wuphilipp/gello_mechanical/gripper/trigger.STL

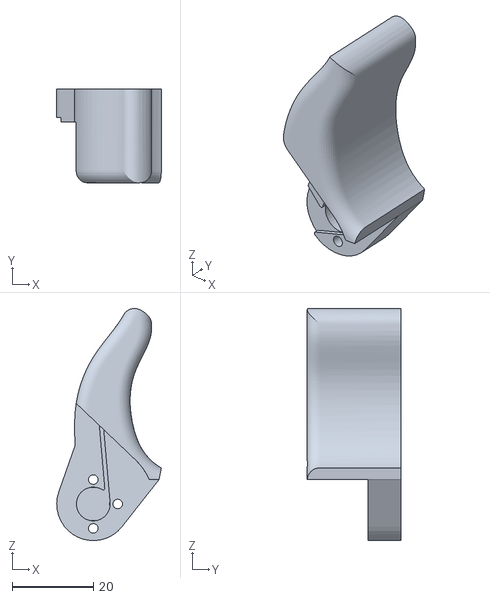
[picture p20: CAD file, 2023-11-06]
gripper/trigger.STL
25.7 x 23.0 x 57.0
