wuphilipp/gello_mechanical/lite6/3dprint_parts/baseRoll.stl

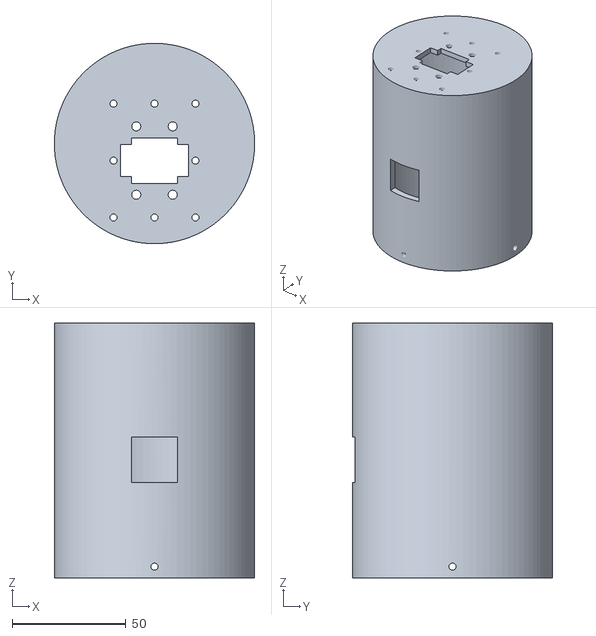
[picture p21: CAD file, 2024-01-16]
lite6/3dprint_parts/baseRoll.stl
88.0 x 88.0 x 112.0
