wuphilipp/gello_mechanical/yam/yam_passive_gello_small/L2.stl

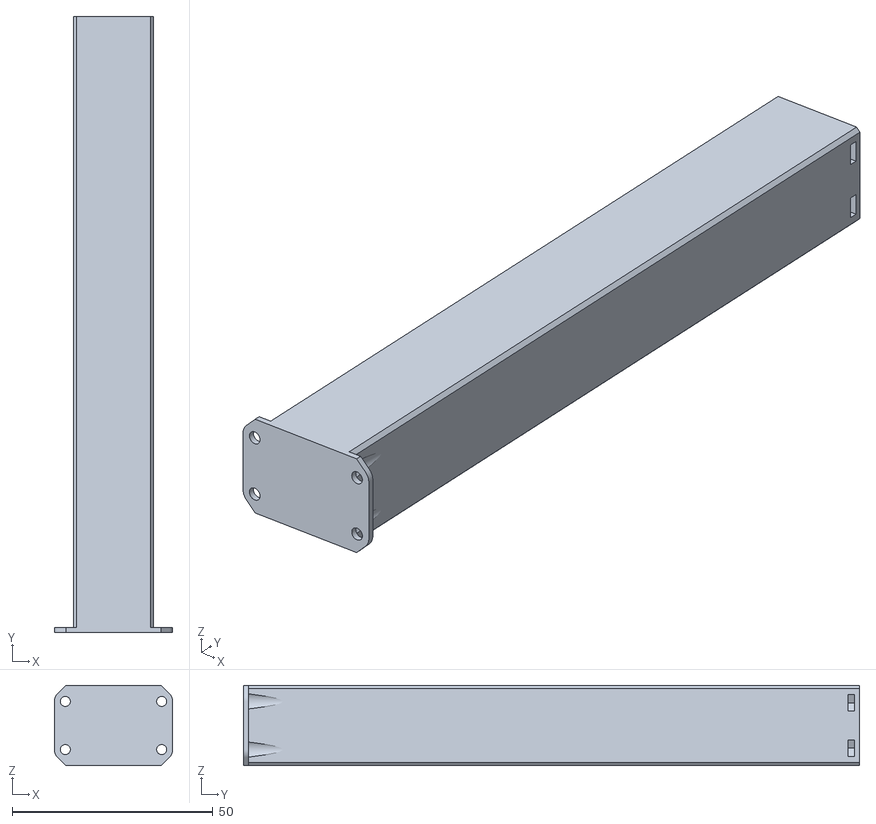
[picture p22: CAD file, 2025-08-02]
yam/yam_passive_gello_small/L2.stl
29.5 x 153.5 x 20.0
