wuphilipp/gello_mechanical/ar4/3dprint_parts/wrist.stl

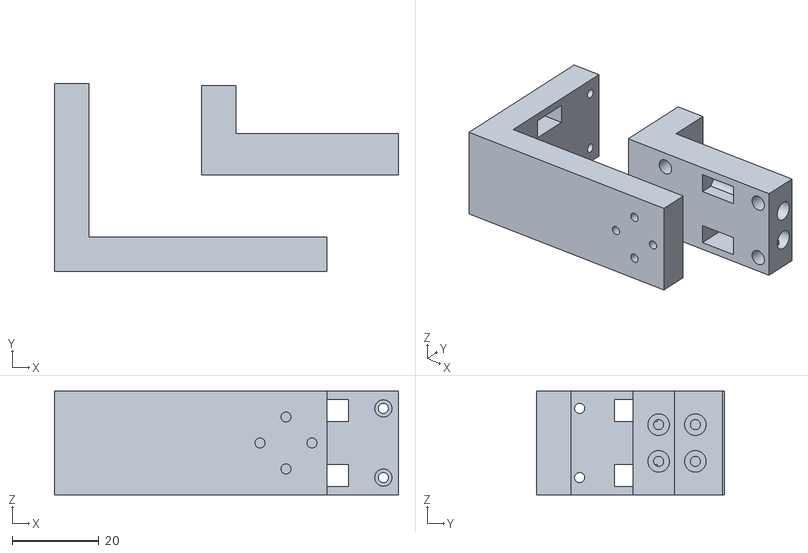
[picture p23: CAD file, 2024-03-06]
ar4/3dprint_parts/wrist.stl
79.5 x 43.5 x 24.0
