wuphilipp/gello_mechanical/franka_fer/base.STL

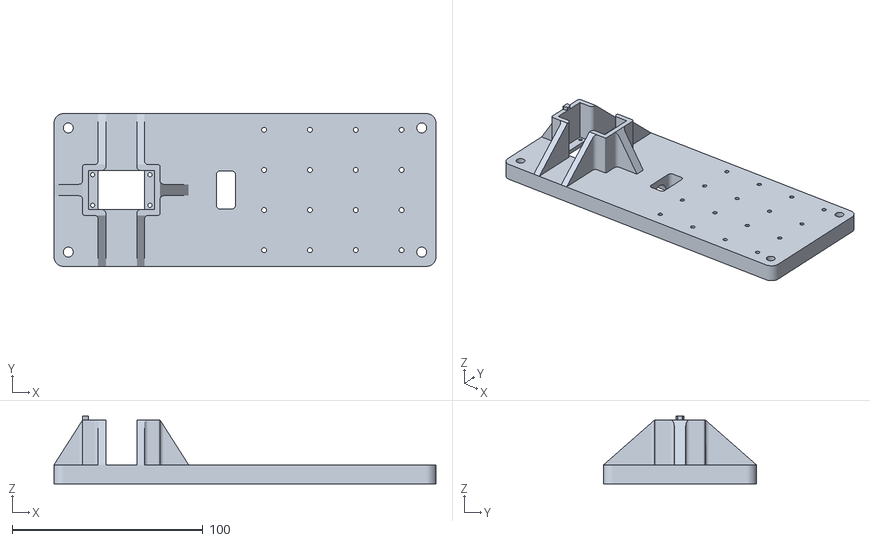
[picture p24: CAD file, 2023-11-06]
franka_fer/base.STL
200.0 x 80.0 x 35.5
