wuphilipp/gello_mechanical/franka_fr3/20_TRIGGER_BODY.STL

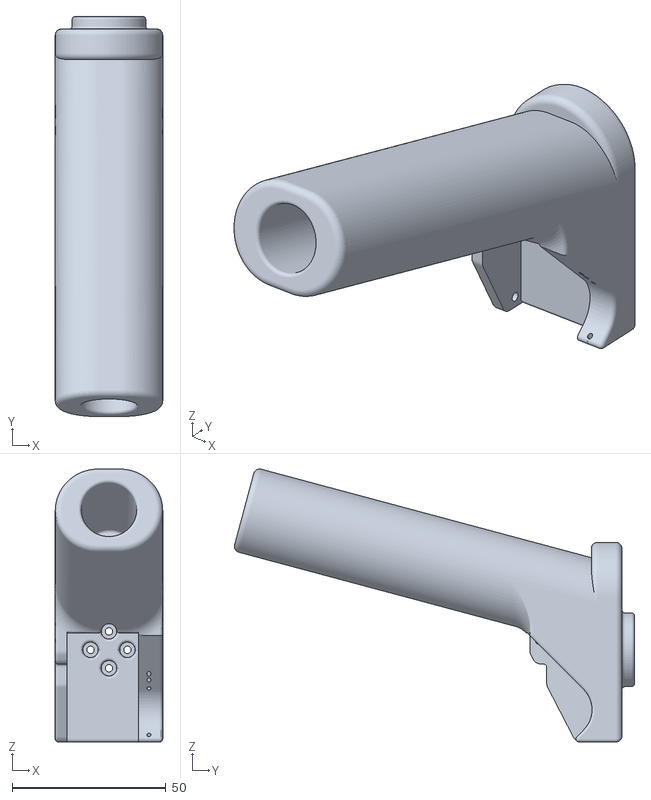
[picture p25: CAD file, 2026-04-10]
franka_fr3/20_TRIGGER_BODY.STL
35.0 x 130.2 x 88.8
