wuphilipp/gello_mechanical/lite6/3dprint_parts/baseBottom.stl

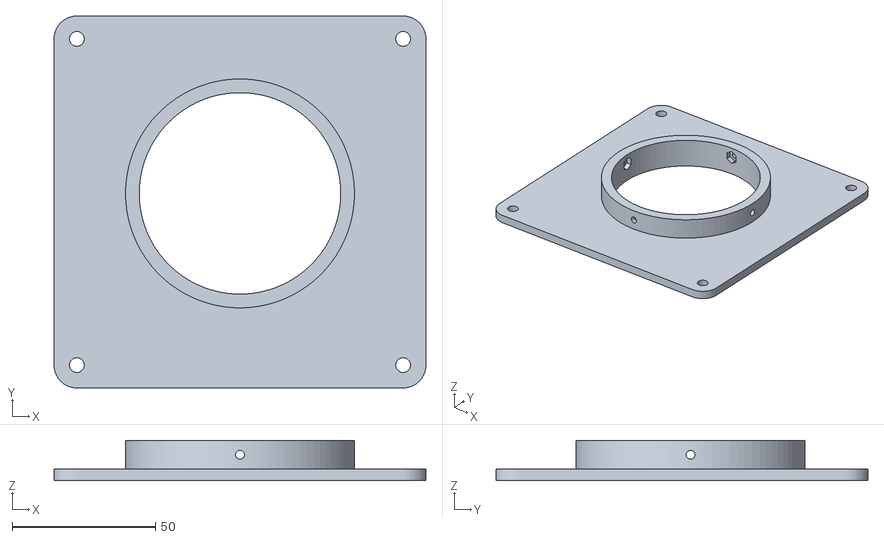
[picture p26: CAD file, 2024-01-16]
lite6/3dprint_parts/baseBottom.stl
130.0 x 130.0 x 14.0
