wuphilipp/gello_mechanical/ar4/3dprint_parts/l1.stl

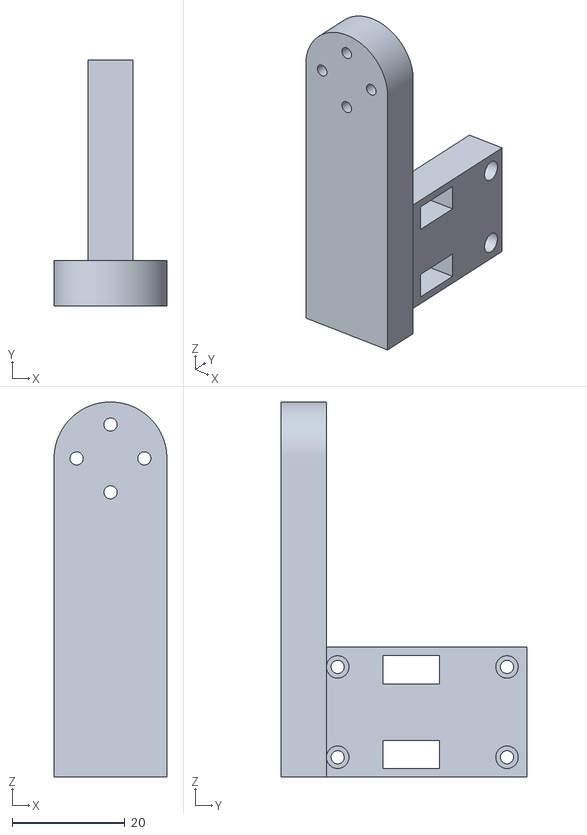
[picture p27: CAD file, 2024-03-06]
ar4/3dprint_parts/l1.stl
20.0 x 43.5 x 66.4
