wuphilipp/gello_mechanical/franka_fer/L2.STL

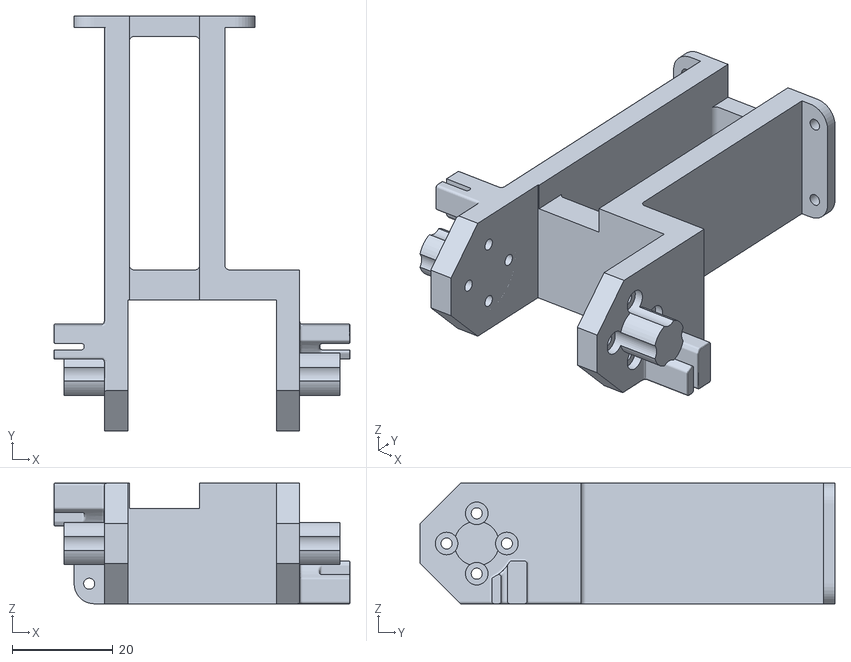
[picture p28: CAD file, 2023-11-06]
franka_fer/L2.STL
58.9 x 82.5 x 24.0
