wuphilipp/gello_mechanical/franka_fr3/02_BASE_BEARING.STL

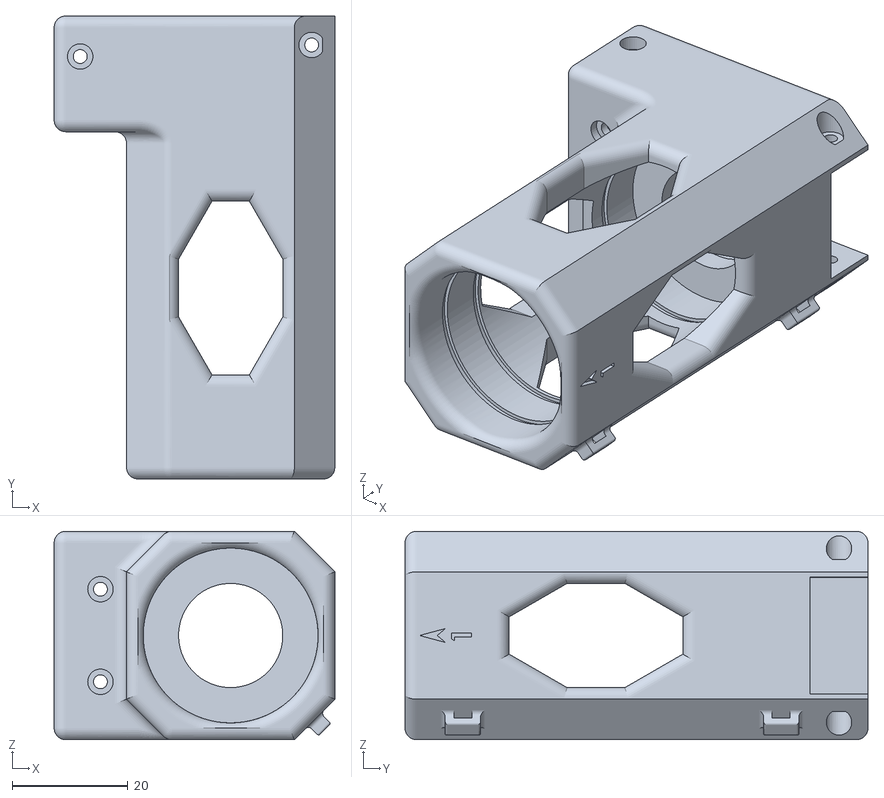
[picture p29: CAD file, 2026-04-10]
franka_fr3/02_BASE_BEARING.STL
48.5 x 80.0 x 36.0
