wuphilipp/gello_mechanical/lite6/3dprint_parts/L2.stl

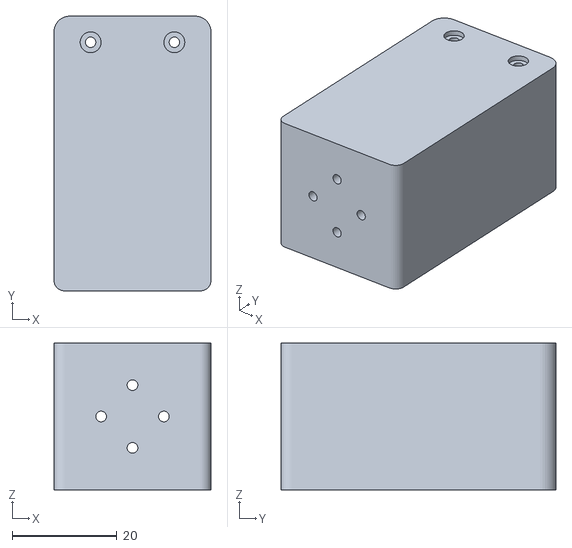
[picture p30: CAD file, 2024-01-16]
lite6/3dprint_parts/L2.stl
30.0 x 52.5 x 28.0
