wuphilipp/gello_mechanical/yam/yam_active_gello/L1.stl

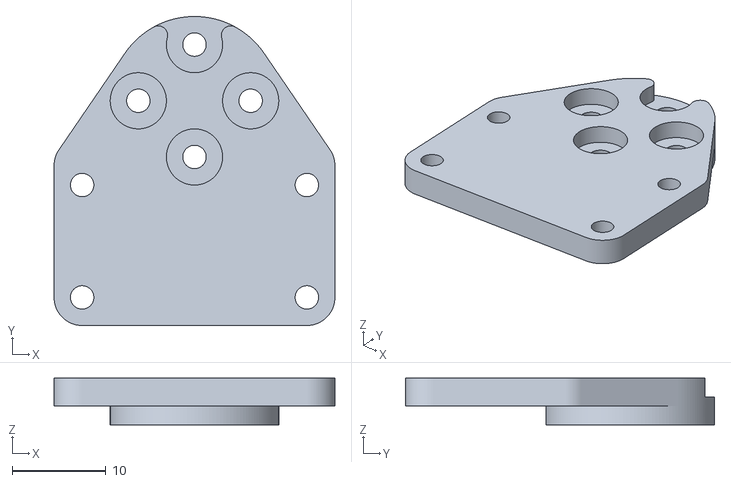
[picture p31: CAD file, 2025-08-02]
yam/yam_active_gello/L1.stl
30.0 x 33.0 x 5.00
