wuphilipp/gello_mechanical/yam/yam_passive_gello_small/L1.stl

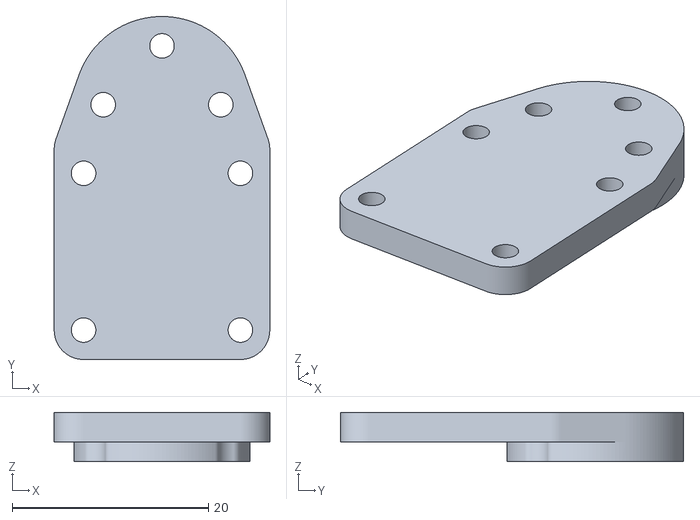
[picture p32: CAD file, 2025-08-02]
yam/yam_passive_gello_small/L1.stl
22.0 x 35.0 x 5.00
