wuphilipp/gello_mechanical/franka_fer/L4.STL

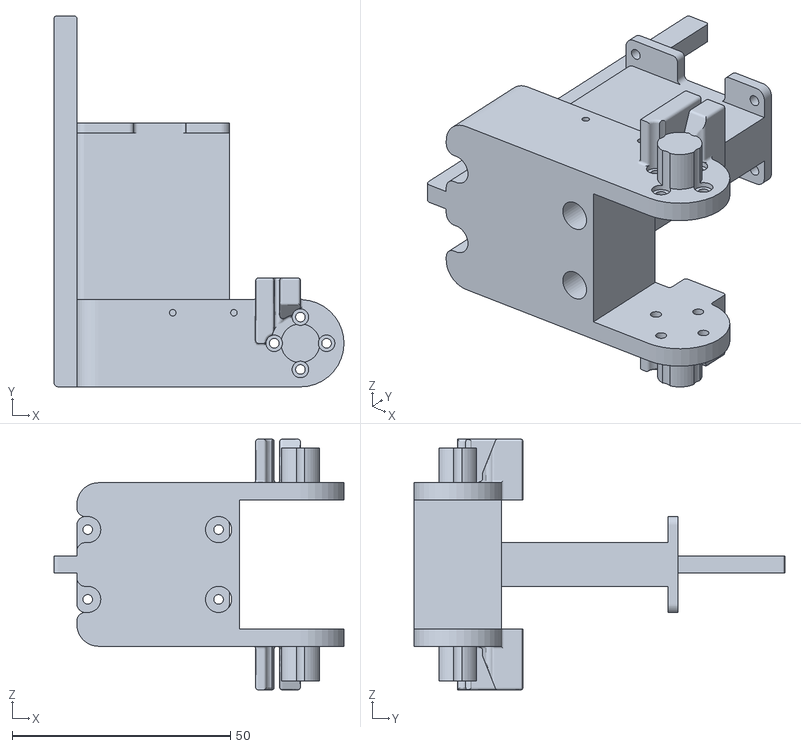
[picture p33: CAD file, 2023-11-06]
franka_fer/L4.STL
66.5 x 85.0 x 57.5
