wuphilipp/gello_mechanical/franka_fr3/11_MOTOR_SHAFT_UNIVERSAL.STL

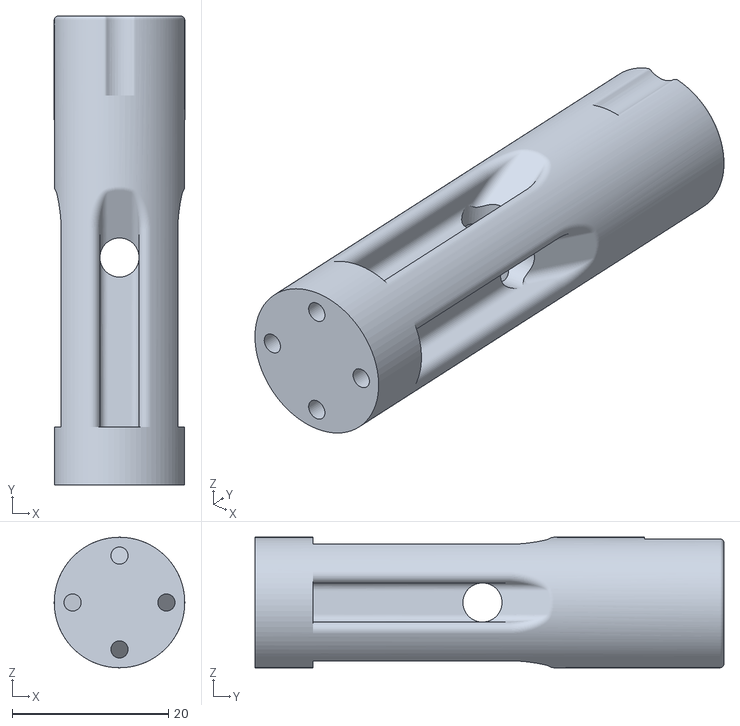
[picture p34: CAD file, 2026-04-10]
franka_fr3/11_MOTOR_SHAFT_UNIVERSAL.STL
16.7 x 60.0 x 16.7
