wuphilipp/gello_mechanical/lite6/3dprint_parts/base.stl

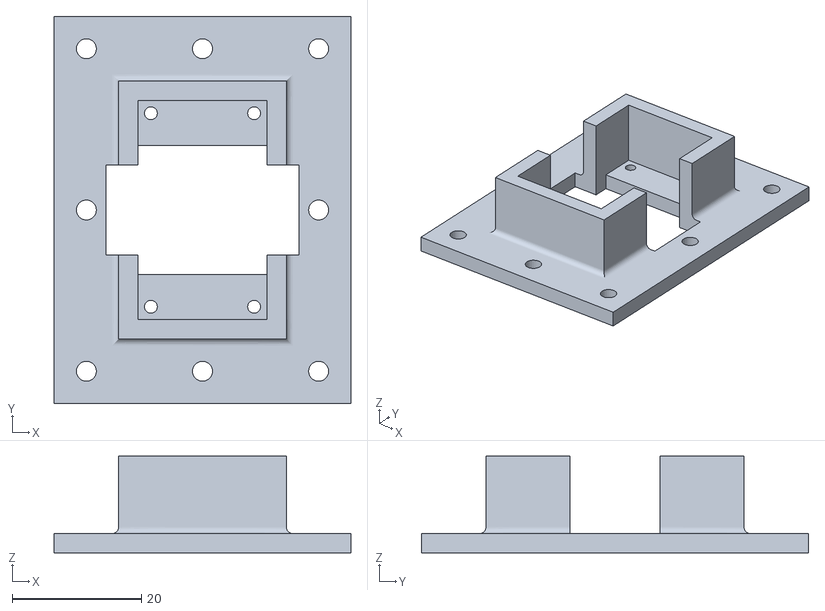
[picture p35: CAD file, 2024-01-16]
lite6/3dprint_parts/base.stl
46.0 x 60.0 x 15.0
