wuphilipp/gello_mechanical/yam/yam_active_gello/L2.stl

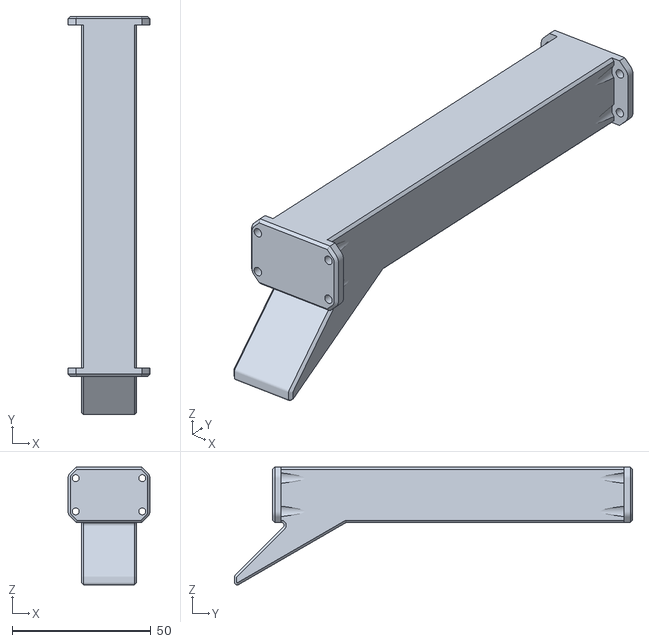
[picture p36: CAD file, 2025-08-02]
yam/yam_active_gello/L2.stl
29.5 x 143.5 x 42.5
