wuphilipp/gello_mechanical/ar4/3dprint_parts/arm2.stl

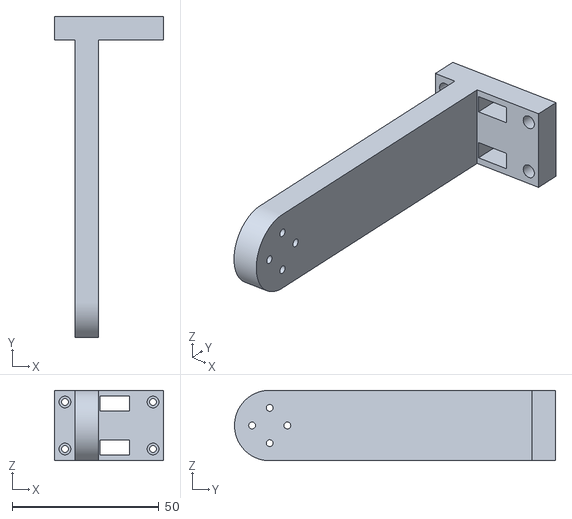
[picture p37: CAD file, 2024-03-06]
ar4/3dprint_parts/arm2.stl
37.0 x 109.3 x 24.0
