wuphilipp/gello_mechanical/franka_fer/L6.STL

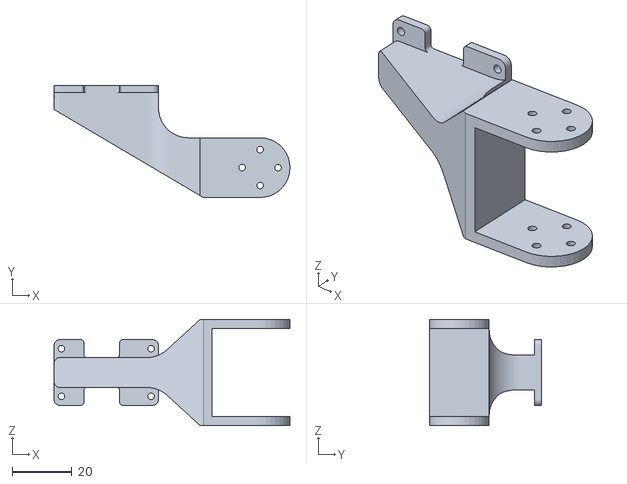
[picture p38: CAD file, 2023-11-06]
franka_fer/L6.STL
79.0 x 37.5 x 35.5
