wuphilipp/gello_mechanical/franka_fr3/03_A12_CONNECTOR.STL

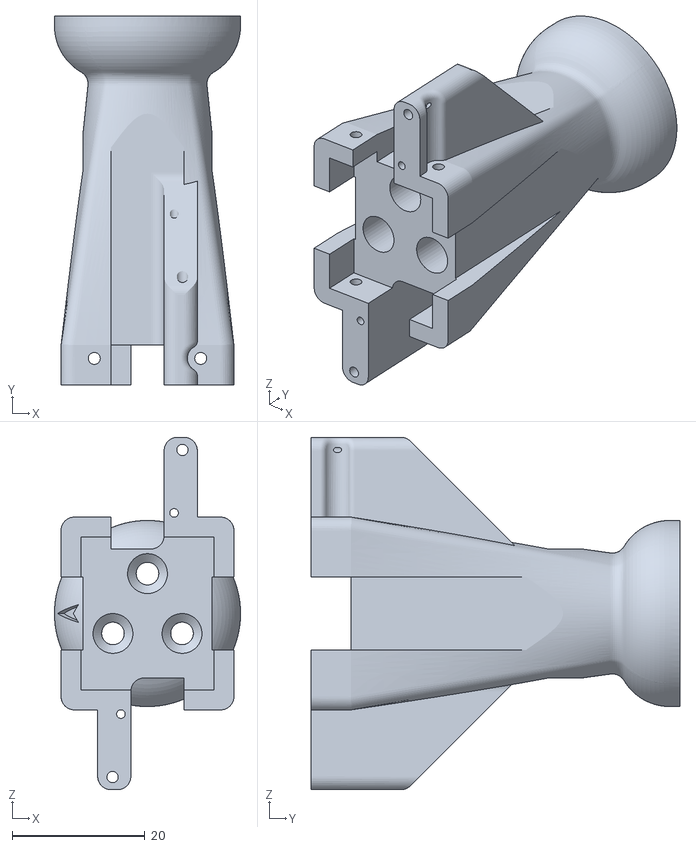
[picture p39: CAD file, 2026-04-10]
franka_fr3/03_A12_CONNECTOR.STL
28.0 x 55.5 x 53.0
