wuphilipp/gello_mechanical/lite6/3dprint_parts/L1.stl

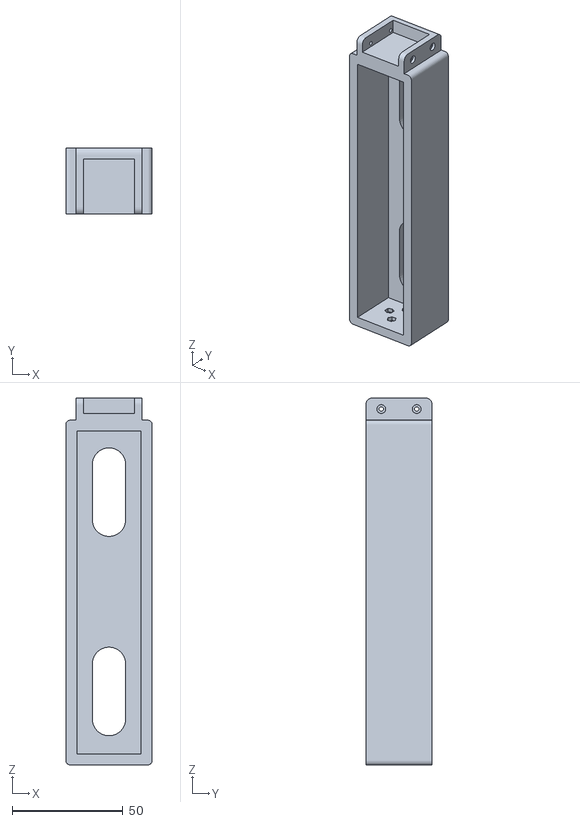
[picture p40: CAD file, 2024-01-16]
lite6/3dprint_parts/L1.stl
39.0 x 30.0 x 165.7
