wuphilipp/gello_mechanical/franka_fer/L3.STL

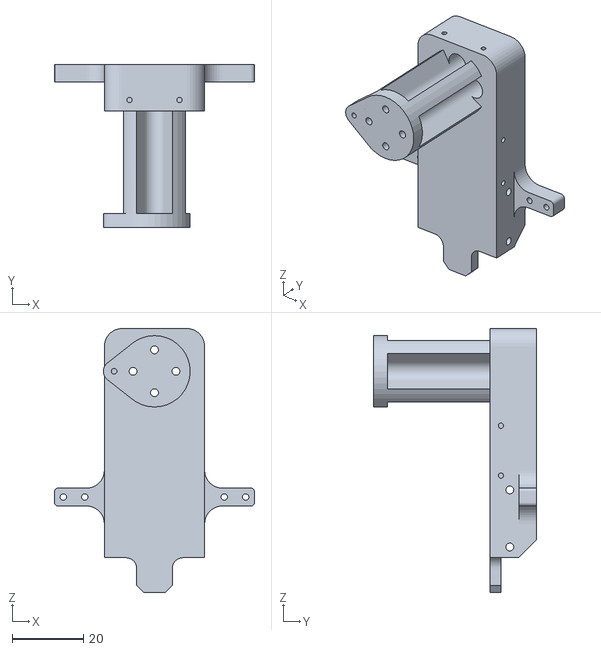
[picture p41: CAD file, 2023-11-06]
franka_fer/L3.STL
56.1 x 45.8 x 74.0
