wuphilipp/gello_mechanical/franka_fr3/21_TRIGGER_FINGER.STL

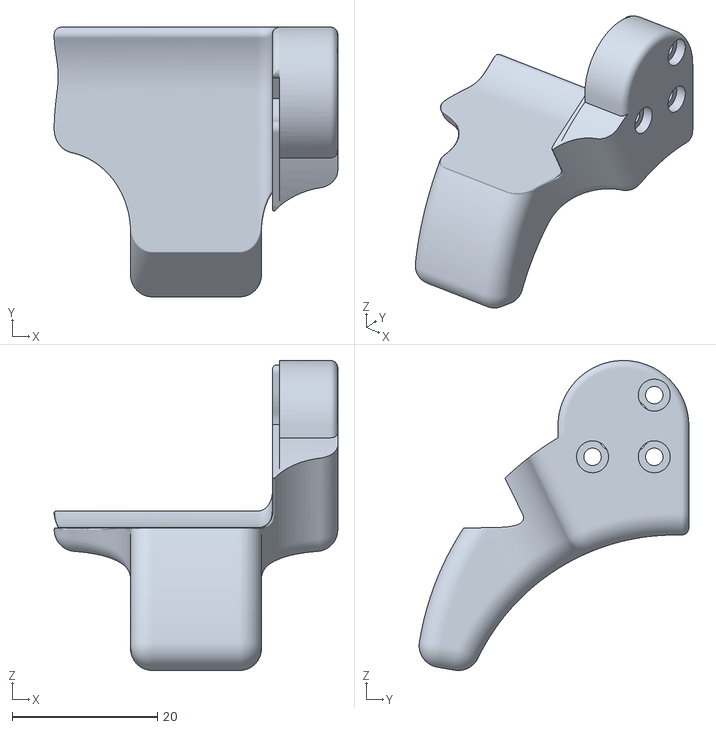
[picture p42: CAD file, 2026-04-10]
franka_fr3/21_TRIGGER_FINGER.STL
39.0 x 37.1 x 42.6
