wuphilipp/gello_mechanical/lite6/3dprint_parts/baseRollExtender.stl

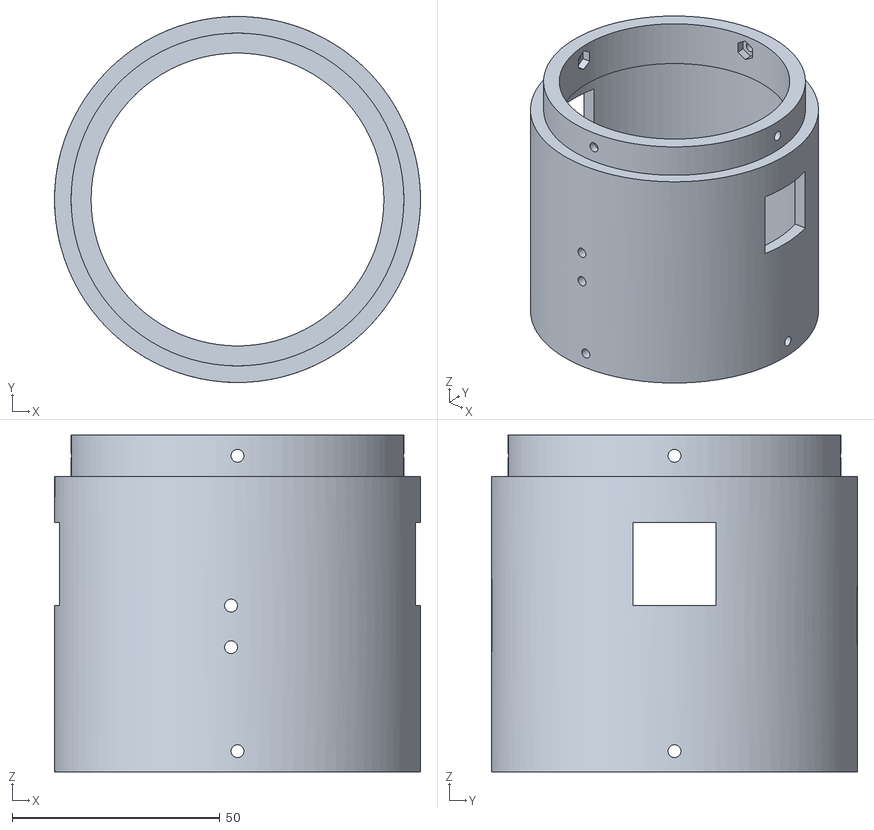
[picture p43: CAD file, 2024-01-16]
lite6/3dprint_parts/baseRollExtender.stl
88.0 x 88.0 x 81.0
