wuphilipp/gello_mechanical/franka_fr3/01_BASE.STL

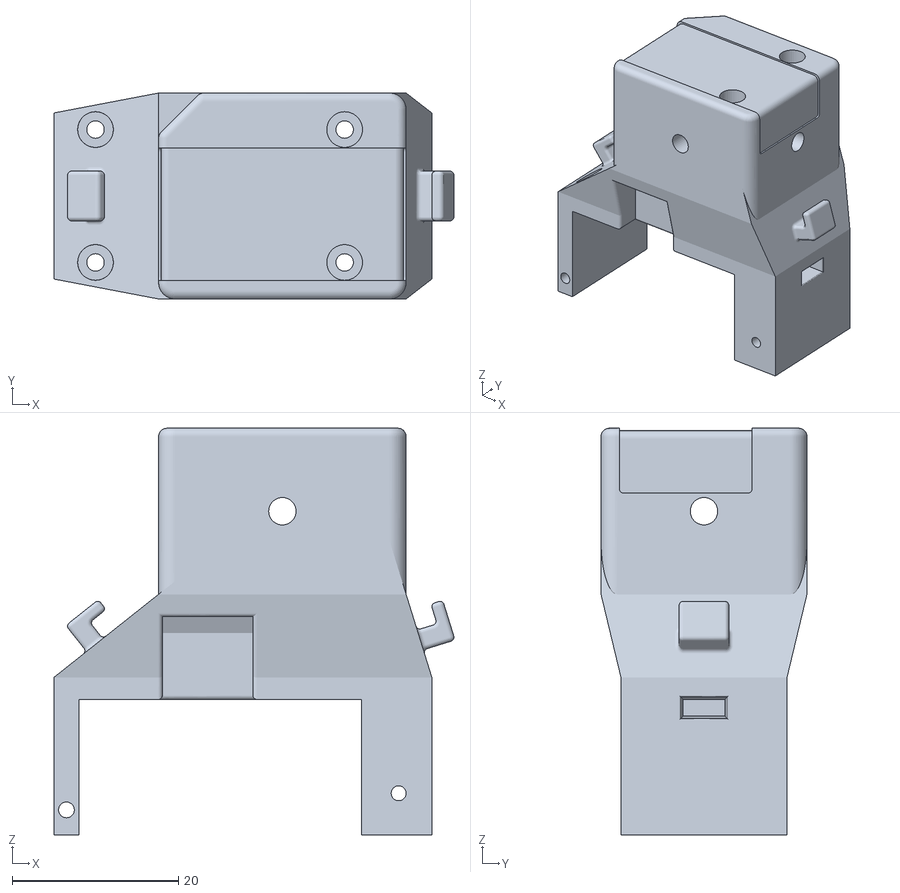
[picture p44: CAD file, 2026-04-10]
franka_fr3/01_BASE.STL
48.2 x 24.8 x 49.0
