wuphilipp/gello_mechanical/lite6/3dprint_parts/L4.stl

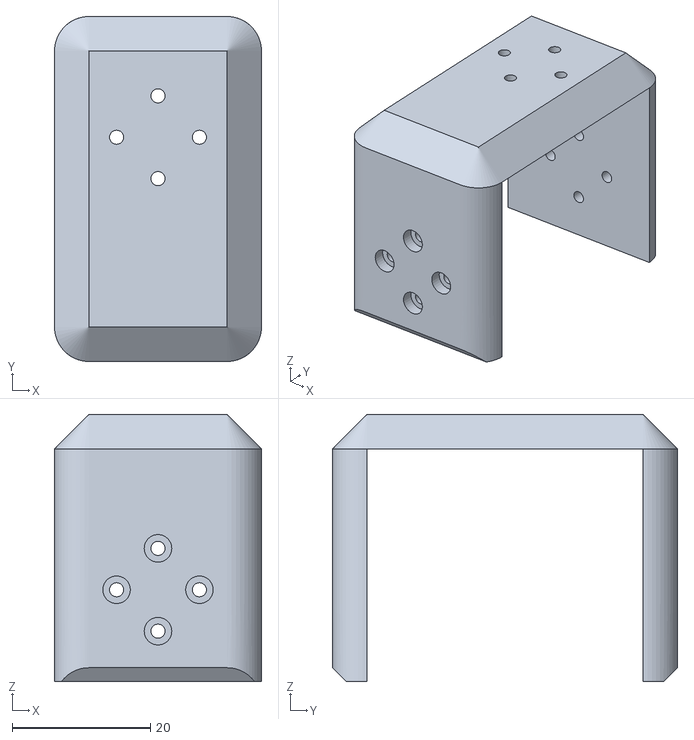
[picture p45: CAD file, 2024-01-16]
lite6/3dprint_parts/L4.stl
30.0 x 50.0 x 38.7
