wuphilipp/gello_mechanical/franka_fr3/08_A67_CONNECTOR.STL

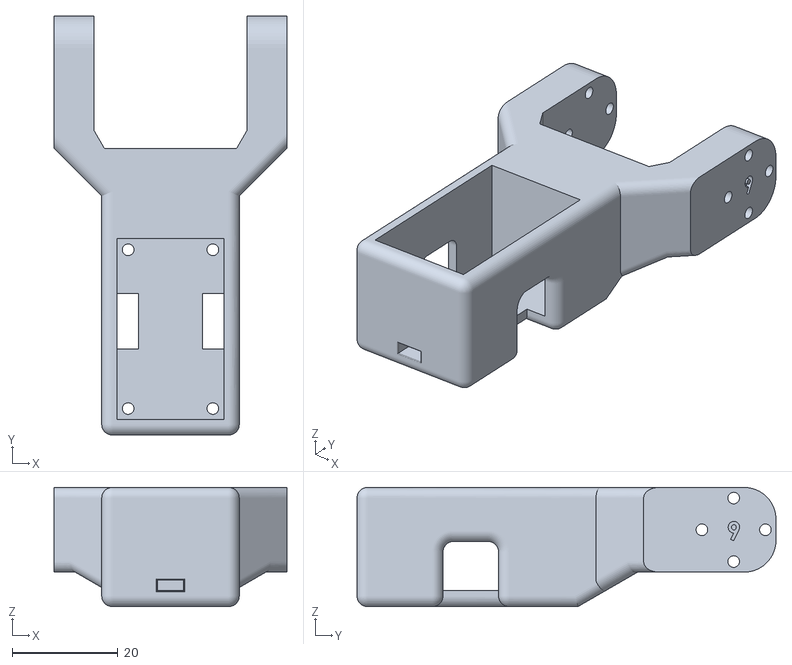
[picture p46: CAD file, 2026-04-10]
franka_fr3/08_A67_CONNECTOR.STL
44.0 x 79.2 x 22.5
