wuphilipp/gello_mechanical/franka_fr3/04_A23_MOTOR_FLANGE.STL

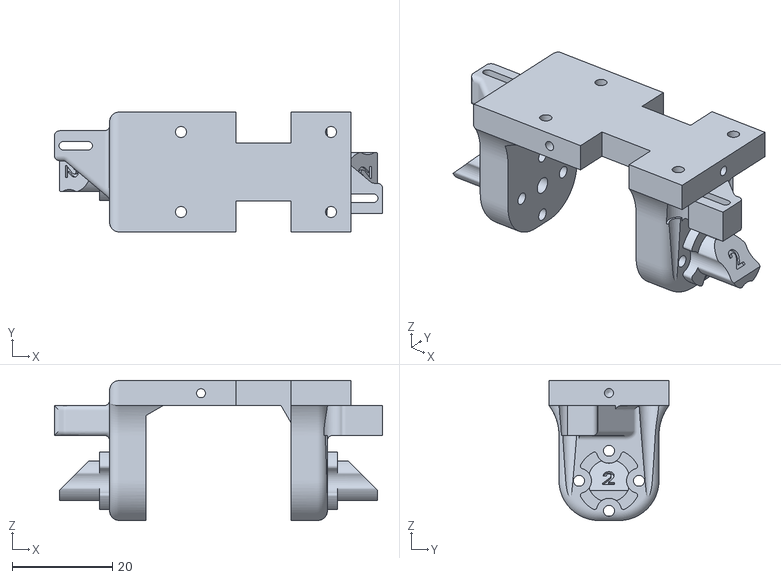
[picture p47: CAD file, 2026-04-10]
franka_fr3/04_A23_MOTOR_FLANGE.STL
65.6 x 24.0 x 28.0
