wuphilipp/gello_mechanical/franka_fr3/00_TABLE_BASE_MOUNT_DUO.STL

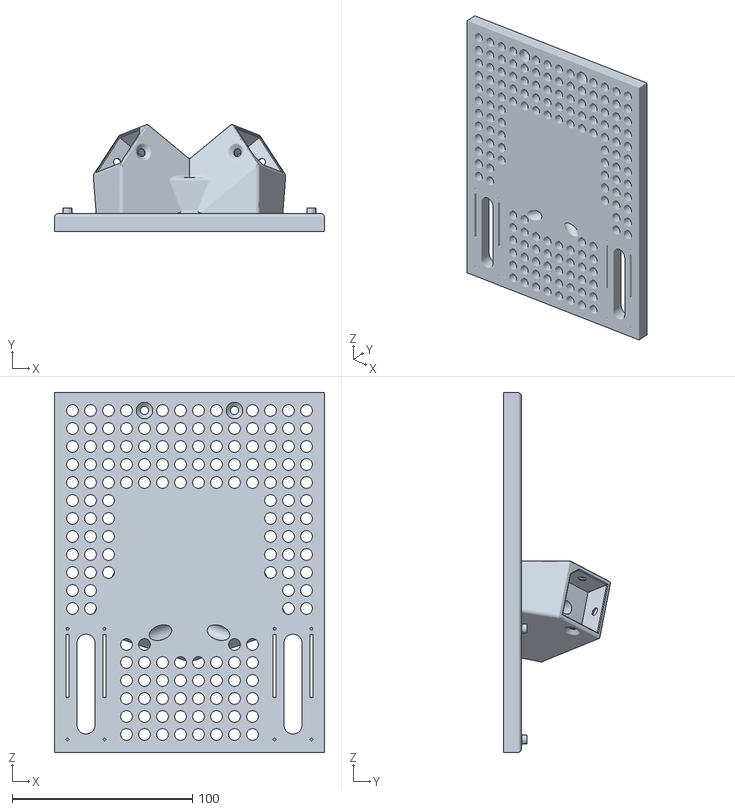
[picture p48: CAD file, 2026-04-10]
franka_fr3/00_TABLE_BASE_MOUNT_DUO.STL
150.0 x 59.5 x 200.0
