wuphilipp/gello_mechanical/franka_fr3/05_A34_CORNER_LINK.STL

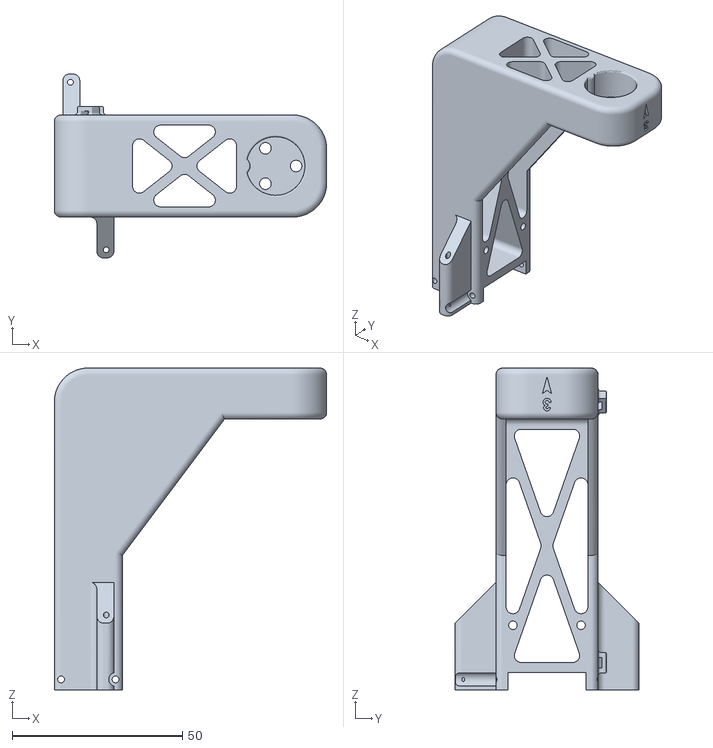
[picture p49: CAD file, 2026-04-10]
franka_fr3/05_A34_CORNER_LINK.STL
80.0 x 54.0 x 94.5
