wuphilipp/gello_mechanical/franka_fr3/12_BEARING_UNIVERSAL.STL

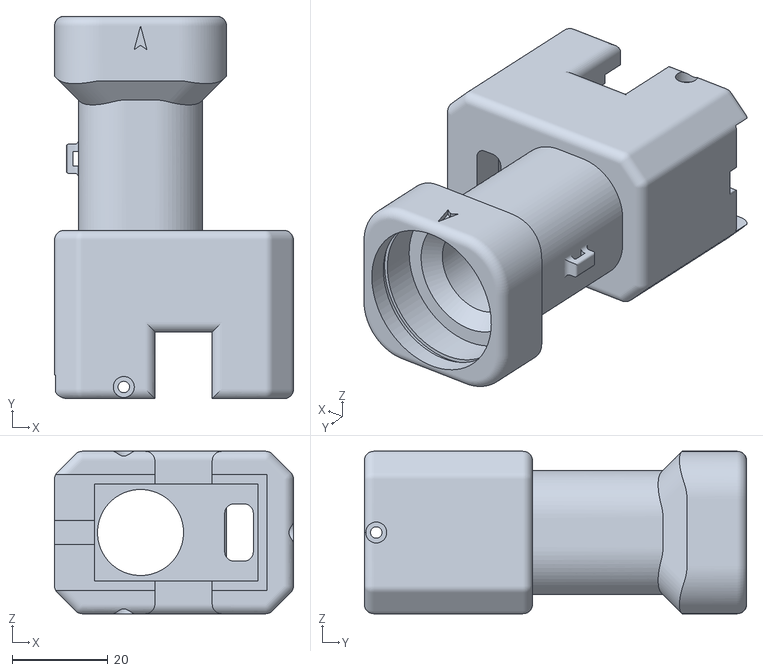
[picture p50: CAD file, 2026-04-10]
franka_fr3/12_BEARING_UNIVERSAL.STL
50.0 x 80.0 x 34.0
