wuphilipp/gello_mechanical/franka_fr3/09_LIMIT_STOP_BACK.STL

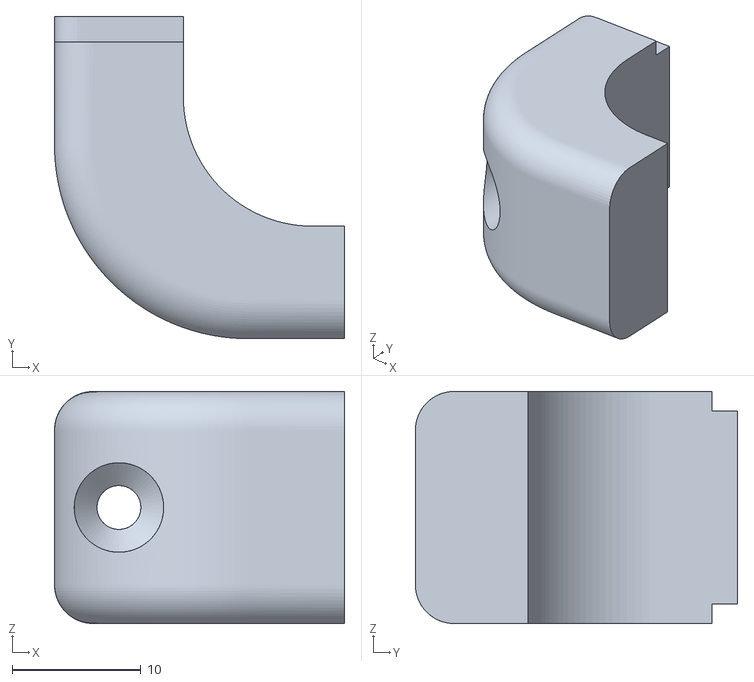
[picture p51: CAD file, 2026-04-10]
franka_fr3/09_LIMIT_STOP_BACK.STL
22.5 x 25.0 x 18.0
