wuphilipp/gello_mechanical/franka_fr3/23_TRIGGER_STORAGE_45.STL

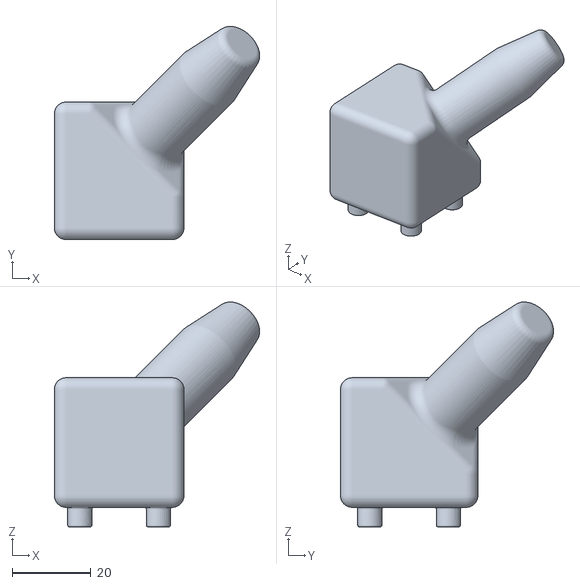
[picture p52: CAD file, 2026-04-10]
franka_fr3/23_TRIGGER_STORAGE_45.STL
52.3 x 54.2 x 57.3
