wuphilipp/gello_mechanical/franka_fr3/00_TABLE_BASE_MOUNT_SINGLE.STL

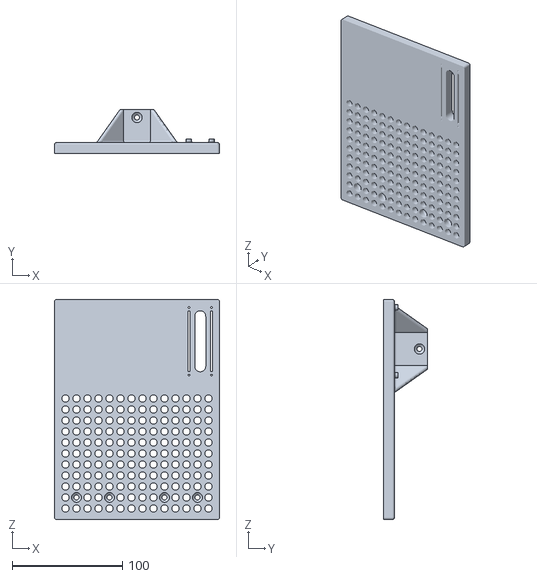
[picture p53: CAD file, 2026-04-10]
franka_fr3/00_TABLE_BASE_MOUNT_SINGLE.STL
150.0 x 40.0 x 200.0
