wuphilipp/gello_mechanical/franka_fr3/06_A45_CORNER_LINK.STL

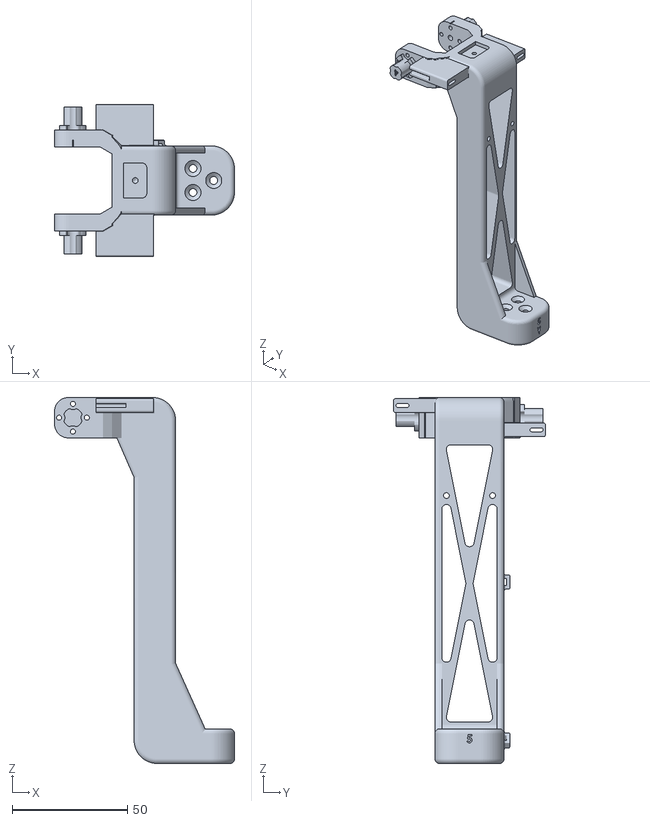
[picture p54: CAD file, 2026-04-10]
franka_fr3/06_A45_CORNER_LINK.STL
78.0 x 66.0 x 158.6
