wuphilipp/gello_mechanical/ar4/l1.scad

use <gello-ar4.scad>;

rotate([-90, 0, 0])
l1();
