wuphilipp/gello_mechanical/ar4/wrist.scad

$fa = 1;
$fs = 0.4;

use <gello-ar4.scad>;

wrist();
